hotkeysoft/ledMatrixGame-kicad/src/LEDMatrixGame/rom.h

const uint8_t rom[] PROGMEM = {
	0x7F, 0x0A, 0x4E, 0x0C, 0x04, 0x83, 0x7F, 0x28, 0xCE, 0x2C, 0xCE, 0x2A, 0xCE, 0x2E, 0x4F, 0x24, 
	0x8F, 0x09, 0x24, 0x92, 0x0F, 0x14, 0xBC, 0xC6, 0x2D, 0x40, 0x33, 0xE3, 0x41, 0x6F, 0x28, 0x45, 
	0x6E, 0x18, 0x80, 0x2A, 0x4B, 0x7F, 0x7B, 0x24, 0xA7, 0x2E, 0x4E, 0x24, 0xAB, 0x0F, 0x00, 0x00, 
	0x00, 0x00, 0x00, 0x00, 0x00, 0x00, 0x00, 0x00, 0x00, 0x00, 0x00, 0x00, 0x00, 0x00, 0x00, 0x00, 
	0x46, 0x29, 0x69, 0x69, 0x69, 0x40, 0x68, 0x13, 0xC0, 0x18, 0x0B, 0x1C, 0xCA, 0x2C, 0x45, 0x3E, 
	0x27, 0x28, 0x21, 0x2C, 0x41, 0x27, 0x11, 0xC0, 0x79, 0xA4, 0x70, 0x9D, 0x8D, 0x29, 0x40, 0x3E, 
	0x27, 0x76, 0x86, 0x87, 0x2C, 0x45, 0x21, 0x04, 0x27, 0x18, 0x0B, 0x1C, 0xD0, 0x1F, 0xF2, 0x29, 
	0x40, 0x07, 0x77, 0xB8, 0x14, 0x0B, 0x12, 0x80, 0x77, 0xBB, 0xB4, 0x77, 0xBE, 0xB4, 0x14, 0x80, 
	0x48, 0x77, 0x87, 0x1C, 0x0B, 0x18, 0x80, 0x77, 0x8D, 0x1C, 0x0B, 0x18, 0x87, 0x77, 0x93, 0x1C, 
	0x0B, 0x19, 0x80, 0x77, 0x99, 0x14, 0x0B, 0x1D, 0x80, 0x18, 0x0B, 0x1E, 0x80, 0x4C, 0x1F, 0xC5, 
	0x18, 0x0B, 0x1C, 0xC0, 0xB5, 0x4C, 0x1F, 0xC5, 0x12, 0xC0, 0x3D, 0xB1, 0x18, 0x0B, 0x1F, 0xE6, 
	0xB5, 0x18, 0x0B, 0x14, 0xDF, 0x2D, 0x42, 0x60, 0x50, 0xB7, 0x1C, 0x80, 0x11, 0xBD, 0x00, 0x00, 
	0x4A, 0x13, 0xCA, 0x2B, 0x40, 0x6F, 0x6F, 0x6F, 0x0F, 0x46, 0x1F, 0xCC, 0x46, 0x1F, 0xC5, 0x2E, 
	0x49, 0x60, 0x60, 0x16, 0xF8, 0x11, 0xC0, 0x2E, 0x45, 0x39, 0xB6, 0x3A, 0xBA, 0x38, 0x80, 0x49, 
	0x3A, 0xBE, 0x2B, 0x40, 0x07, 0xB4, 0x27, 0x48, 0x07, 0xB4, 0x27, 0x44, 0x07, 0xB4, 0xC3, 0x18, 
	0x0B, 0x1C, 0xCA, 0x93, 0x27, 0x93, 0x1D, 0xEB, 0x18, 0xA9, 0x1D, 0xEB, 0x18, 0x80, 0x41, 0x81, 
	0x29, 0x4A, 0x21, 0x41, 0x01, 0x87, 0x96, 0x00, 0x98, 0x42, 0x21, 0x4E, 0x01, 0x8F, 0x96, 0x00, 
	0x98, 0x4C, 0x21, 0x46, 0x01, 0x98, 0x7F, 0x0F, 0x7F, 0x70, 0x0F, 0x29, 0x3E, 0x25, 0x7A, 0xAA, 
	0x44, 0x21, 0x2D, 0x24, 0x29, 0x21, 0x2D, 0x27, 0x15, 0x8B, 0x3E, 0x25, 0x7A, 0xB2, 0x4C, 0x7F, 
	0x24, 0xA0, 0x3E, 0x27, 0x7A, 0xBA, 0x04, 0x7F, 0x24, 0xB0, 0x4C, 0x69, 0x69, 0x69, 0x14, 0x9D, 
	0x3E, 0x0A, 0x4B, 0x2C, 0x38, 0x87, 0x0F, 0x34, 0x3B, 0x8C, 0x1F, 0xF2, 0x37, 0x7F, 0x7B, 0x4F, 
	0x2E, 0x26, 0x2A, 0x25, 0x21, 0x70, 0xBE, 0x70, 0xA0, 0x05, 0x3B, 0xA0, 0x21, 0x04, 0x16, 0x80, 
	0x2A, 0x4F, 0x21, 0x7C, 0xA9, 0x7B, 0x27, 0x20, 0x94, 0x2E, 0x21, 0x78, 0x27, 0xA7, 0x21, 0x76, 
	0xB7, 0x7E, 0xB5, 0x40, 0xB6, 0x20, 0x0F, 0x4E, 0x77, 0xBC, 0x04, 0xB6, 0x77, 0x0F, 0x16, 0xB8, 
	0x77, 0x87, 0xEF, 0x28, 0x30, 0x1A, 0xA0, 0x77, 0x90, 0x1A, 0xEE, 0x28, 0x78, 0x84, 0x32, 0x85, 
	0x77, 0x96, 0xEF, 0x28, 0x31, 0x85, 0x77, 0x9F, 0x1A, 0xEE, 0x28, 0x78, 0x94, 0x33, 0x85, 0x77, 
	0xA4, 0xEF, 0x2C, 0x84, 0x77, 0xAC, 0x1A, 0xEE, 0x2C, 0x78, 0x84, 0x8E, 0xEF, 0x2C, 0x94, 0x21, 
	0x4A, 0x76, 0xB7, 0x04, 0x78, 0xB7, 0xB3, 0x0F, 0x28, 0x45, 0x07, 0xBD, 0x76, 0x27, 0x1E, 0x80, 
	0x7D, 0x84, 0x21, 0x85, 0x2C, 0x4E, 0x77, 0x94, 0x7F, 0x0A, 0x38, 0x90, 0x0C, 0x04, 0x8A, 0xBB, 
	0x0D, 0x04, 0x8A, 0xBB, 0x77, 0xA2, 0x7F, 0x0A, 0x3A, 0x9E, 0x0C, 0x04, 0x98, 0xBB, 0x0D, 0x04, 
	0x98, 0xBB, 0x77, 0xB0, 0x7F, 0x0A, 0x39, 0xAC, 0x0C, 0x04, 0xA6, 0xBB, 0x0D, 0x04, 0xA6, 0xBB, 
	0x7F, 0x0A, 0x3B, 0xB8, 0x0C, 0x04, 0xB2, 0xBB, 0x0D, 0x04, 0xB2, 0x45, 0x28, 0x1A, 0x80, 0x00, 
	0x16, 0xF8, 0x28, 0x47, 0x69, 0x47, 0x22, 0x0D, 0x08, 0x0C, 0x3D, 0xAB, 0x3D, 0x09, 0x26, 0x38, 
	0xB7, 0x2E, 0x34, 0x29, 0x3A, 0xB9, 0x2E, 0x36, 0x29, 0x39, 0xBB, 0x2E, 0x35, 0x29, 0xAD, 0x3A, 
	0xA5, 0x32, 0x4B, 0x27, 0xB3, 0x36, 0x4B, 0x00, 0xB3, 0x43, 0xB5, 0x2E, 0x60, 0x28, 0x47, 0x3A, 
	0xB3, 0x65, 0x85, 0x43, 0x7F, 0x27, 0x0F, 0x19, 0x80, 0x19, 0x91, 0x19, 0xA2, 0x15, 0xBB, 0x00, 
	0x70, 0x2E, 0x38, 0x8E, 0x28, 0x41, 0x3A, 0x89, 0xB2, 0x47, 0x22, 0x2E, 0x30, 0xB2, 0xFA, 0x11, 
	0x94, 0x78, 0x2E, 0x3A, 0x9F, 0x28, 0x41, 0x3A, 0x9A, 0xB2, 0x47, 0x22, 0x2E, 0x32, 0xB2, 0xFA, 
	0x11, 0x99, 0x74, 0x2E, 0x39, 0xB0, 0x28, 0x41, 0x3A, 0xAB, 0xB2, 0x47, 0x22, 0x2E, 0x31, 0xB2, 
	0x11, 0xAD, 0x28, 0x47, 0x38, 0xB7, 0x74, 0x41, 0x11, 0x9F, 0x28, 0x47, 0x22, 0x29, 0x7F, 0x0F, 
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
	};
